ericvoi/OpenAquatix-Hardware/v2/src/3d_models/10118193-0001lfc.step

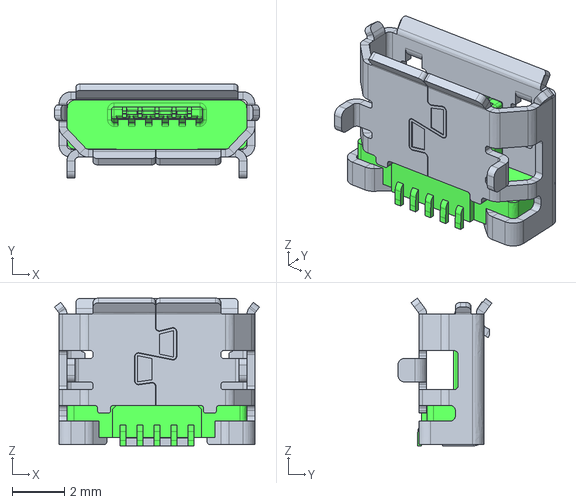
[picture p15: CAD file, 2026-03-23]
v2/src/3d_models/10118193-0001lfc.step
7.86 x 3.60 x 5.66 mm
