ericvoi/OpenAquatix-Hardware/v2/src/3d_models/b82477d4_m900.step

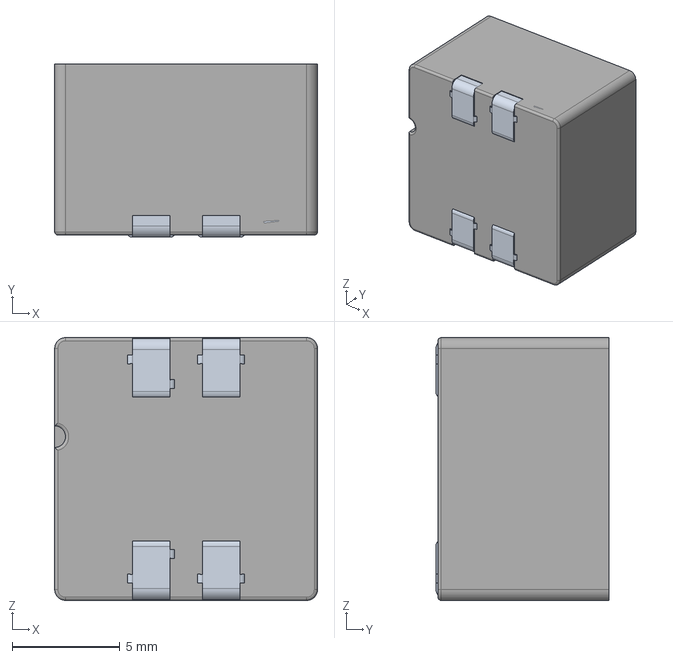
[picture p16: CAD file, 2026-03-23]
v2/src/3d_models/b82477d4_m900.step
12.2 x 8.05 x 12.2 mm
