ericvoi/OpenAquatix-Hardware/v2/src/Calculations/Impedance_Matching.asc

C1: cap; 20n
C2: cap; 1.91n
C3: cap; 10n
C4: cap; 10n
C5: cap; 1n
C6: cap; 1n
C7: cap; 900n; Rser=10m
C8: cap; 900n; Rser=10m
C9: cap; 68n; Rser=10m
C10: cap; 1µ5; Rser=10m
C11: cap; 1µ5; Rser=10m
C12: cap; 1n
C13: cap; 1n
C28: cap; 1n
C31: cap; 1n
L1: ind; 13m3
L2: ind2; 136µ; Rser=480m
L3: ind2; 136µ; Rser=325m
L4: ind; 33µ; Rser=140m
L5: ind; 33µ; Rser=140m
L6: ind; 300µ; Rser=400m
L7: ind; 22µ; Rser=140m
L8: ind; 22µ; Rser=140m
R1: res; 300
R2: res; 150m
R3: res; 3R3
R4: res; 3R3
R5: res; 60m
R6: res; 60m
R7: res; 60m
R8: res; 60m
R9: res; 1Meg
R11: res; 100m
V1: voltage; SINE(13 10 30k 0 0 180); AC 1.65
V2: voltage; SINE(13 10 30k 0 0 0); AC 1.65 180
V3: voltage; SINE(13 10 30k 0 0 180); AC 1.65
V4: voltage; SINE(13 10 30k 0 0 0); AC 1.65 180
Named nets: output4, 0
K1 L2 L3 0.995
;tran 0 2.1m 2m
.ac lin 1000 24k 40k
436.7
